kjlesmes/Llenador-por-Histeresis/Base.JPG

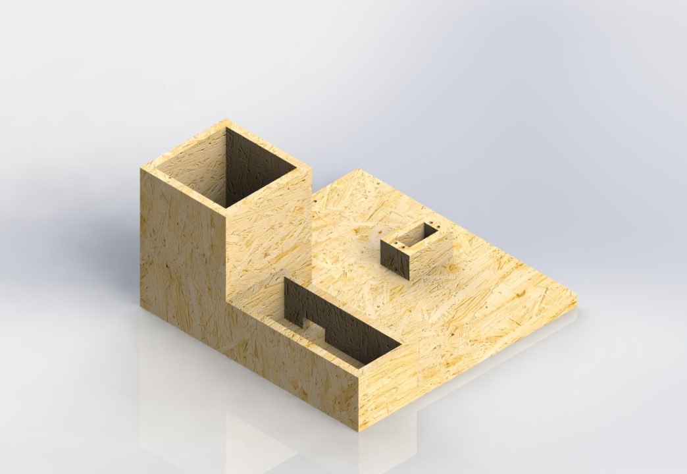
Base.JPG
