kjlesmes/Llenador-por-Histeresis/Plato_Giratorio.JPG

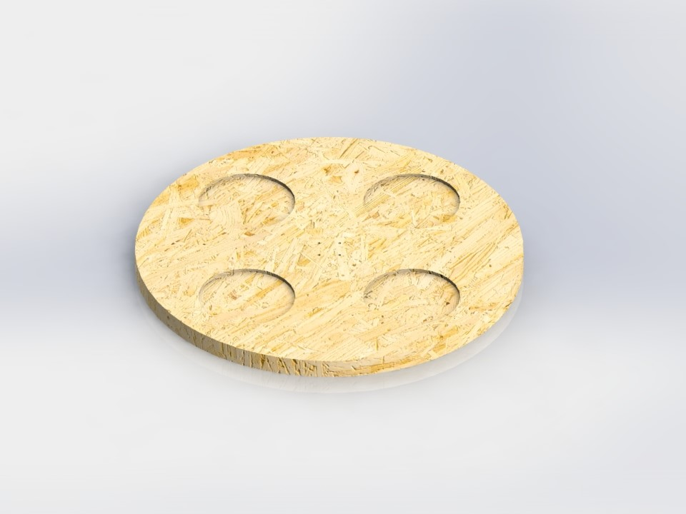
Plato_Giratorio.JPG
