kjlesmes/Llenador-por-Histeresis/Vaso.JPG

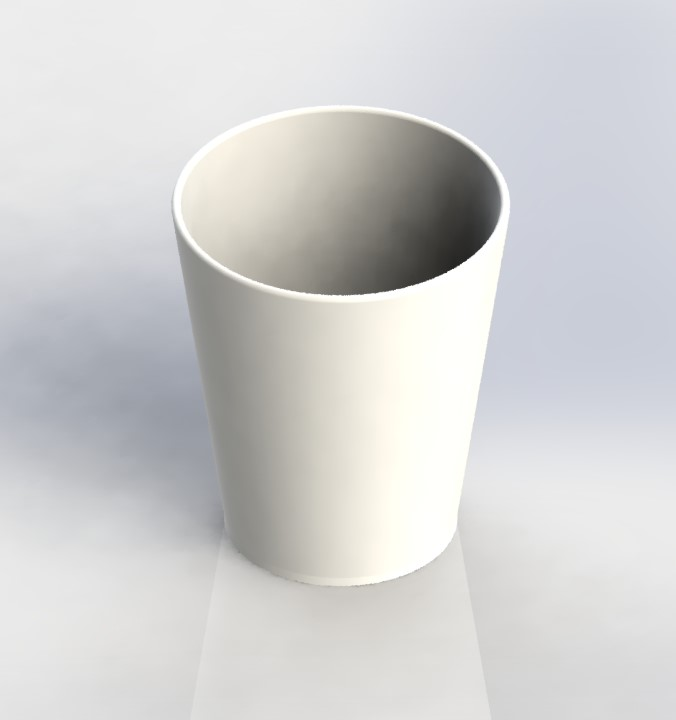
Vaso.JPG
