kjlesmes/Llenador-por-Histeresis/Vista_1.JPG

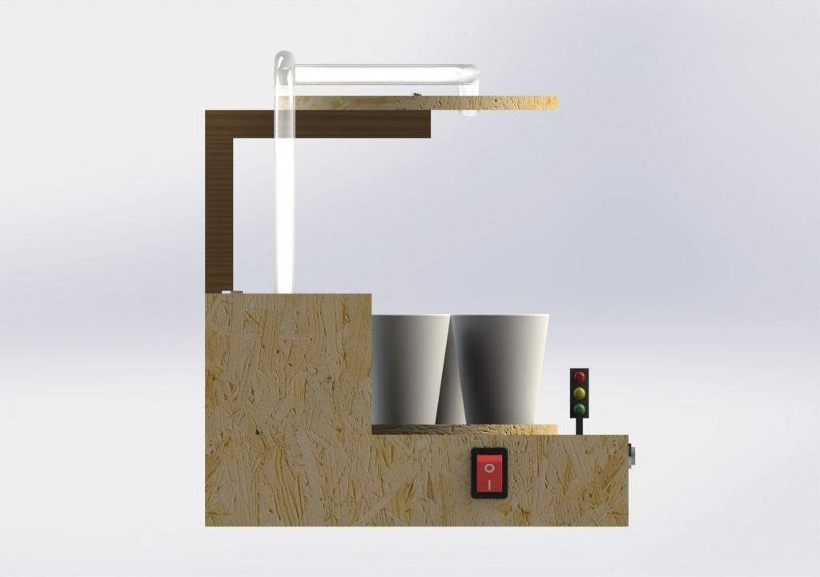
Vista_1.JPG
