kjlesmes/Llenador-por-Histeresis/Vista_2.JPG

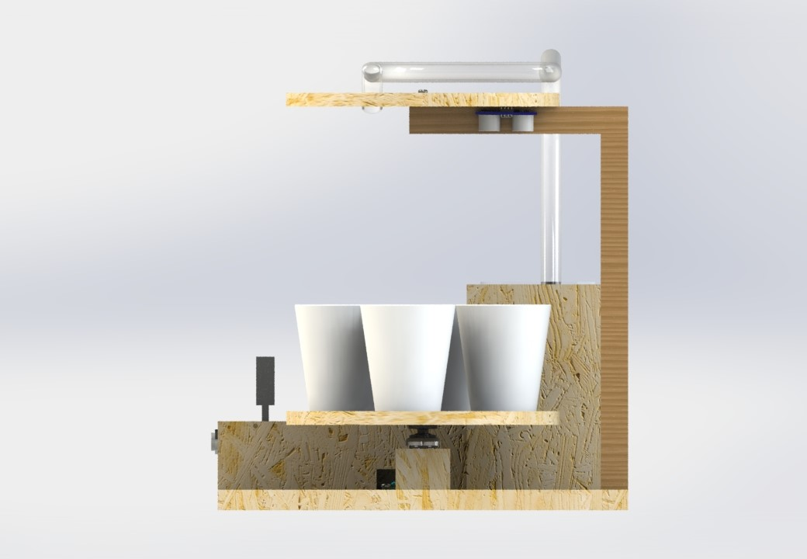
Vista_2.JPG
