kjlesmes/Llenador-por-Histeresis/Vista_3.JPG

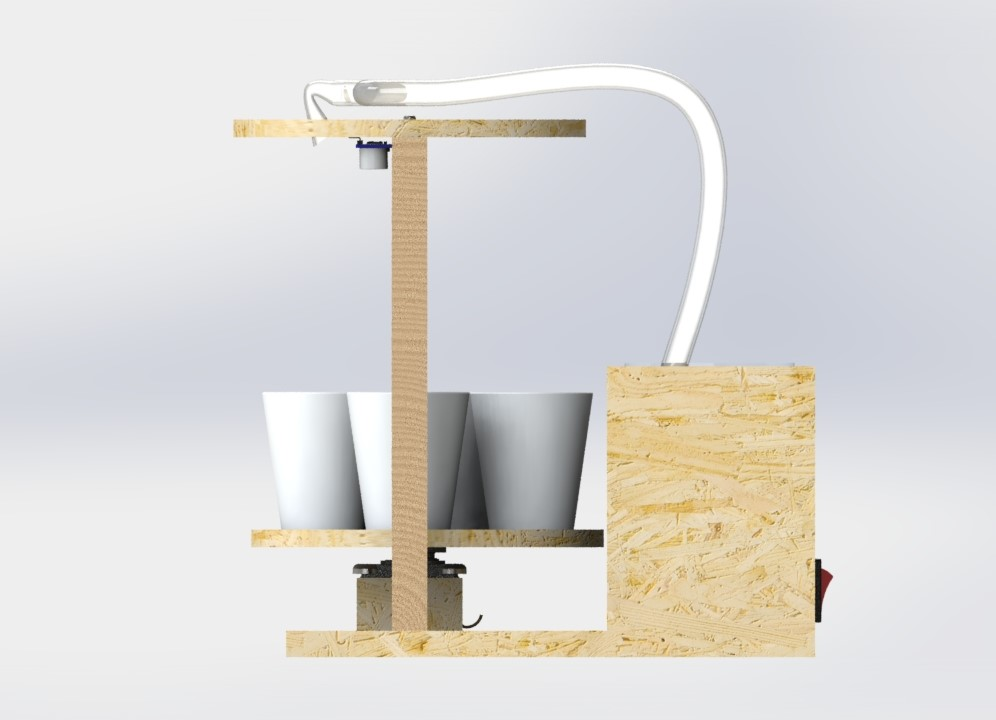
Vista_3.JPG
