kjlesmes/Llenador-por-Histeresis/Vista_4.JPG

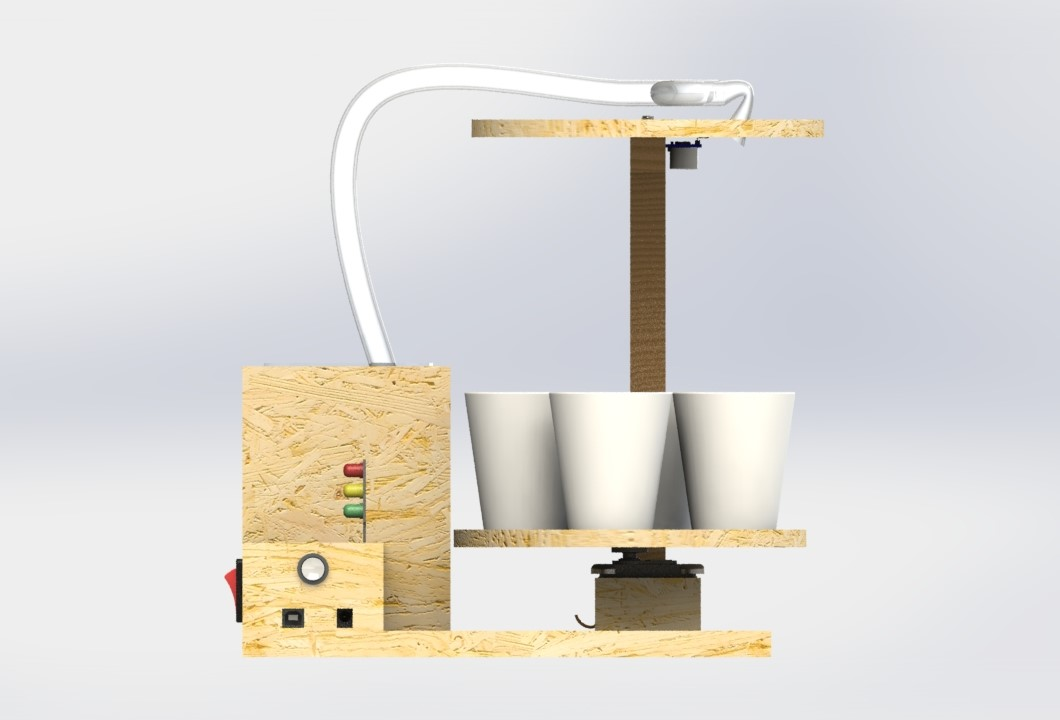
Vista_4.JPG
